diylxy/ESP32-Paperang-Emulator/Program/Printer/crc.cpp

/**
 * \file
 * Functions and types for CRC checks.
 *
 * Generated on Tue Jan  7 07:33:25 2020
 * by pycrc v0.9.2, https://pycrc.org
 * using the configuration:
 *  - Width         = 32
 *  - Poly          = 0x04c11db7
 *  - XorIn         = 0xffffffff
 *  - ReflectIn     = True
 *  - XorOut        = 0xffffffff
 *  - ReflectOut    = True
 *  - Algorithm     = table-driven
 */
#include "crc.h"     /* include the header file generated with pycrc */
#include <stdlib.h>
#include <stdint.h>



/**
 * Static table used for the table_driven implementation.
 */
static const crc_t crc_table[256] = {
    0x00000000, 0x77073096, 0xee0e612c, 0x990951ba, 0x076dc419, 0x706af48f, 0xe963a535, 0x9e6495a3,
    0x0edb8832, 0x79dcb8a4, 0xe0d5e91e, 0x97d2d988, 0x09b64c2b, 0x7eb17cbd, 0xe7b82d07, 0x90bf1d91,
    0x1db71064, 0x6ab020f2, 0xf3b97148, 0x84be41de, 0x1adad47d, 0x6ddde4eb, 0xf4d4b551, 0x83d385c7,
    0x136c9856, 0x646ba8c0, 0xfd62f97a, 0x8a65c9ec, 0x14015c4f, 0x63066cd9, 0xfa0f3d63, 0x8d080df5,
    0x3b6e20c8, 0x4c69105e, 0xd56041e4, 0xa2677172, 0x3c03e4d1, 0x4b04d447, 0xd20d85fd, 0xa50ab56b,
    0x35b5a8fa, 0x42b2986c, 0xdbbbc9d6, 0xacbcf940, 0x32d86ce3, 0x45df5c75, 0xdcd60dcf, 0xabd13d59,
    0x26d930ac, 0x51de003a, 0xc8d75180, 0xbfd06116, 0x21b4f4b5, 0x56b3c423, 0xcfba9599, 0xb8bda50f,
    0x2802b89e, 0x5f058808, 0xc60cd9b2, 0xb10be924, 0x2f6f7c87, 0x58684c11, 0xc1611dab, 0xb6662d3d,
    0x76dc4190, 0x01db7106, 0x98d220bc, 0xefd5102a, 0x71b18589, 0x06b6b51f, 0x9fbfe4a5, 0xe8b8d433,
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
{
    const unsigned char *d = (const unsigned char *)data;
    unsigned int tbl_idx;

    while (data_len--) {
        tbl_idx = (crc ^ *d) & 0xff;
        crc = (crc_table[tbl_idx] ^ (crc >> 8)) & 0xffffffff;
        d++;
    }
    return crc & 0xffffffff;
}
