diylxy/ESP32-Paperang-Emulator/Program/Printer/Arduino_CRC32.cpp

/*
  Copyright (c) 2020 Arduino.  All rights reserved.

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
  You should have received a copy of the GNU Lesser General Public
  License along with this library; if not, write to the Free Software
  Foundation, Inc., 51 Franklin St, Fifth Floor, Boston, MA  02110-1301  USA
*/

/**************************************************************************************
 * INCLUDE
 **************************************************************************************/

#include "Arduino_CRC32.h"

/**************************************************************************************
 * PUBLIC MEMBER FUNCTIONS
 **************************************************************************************/

void Arduino_CRC32::init(uint32_t start)
{
  crc32_start = start;
}

uint32_t Arduino_CRC32::calc(uint8_t const data[], uint32_t const len)
{
  crc_t crc32;
  crc32 = crc_update(crc32_start, data, len);
  crc32 = crc_finalize(crc32);
  return crc32;
}
